dimadl/cosmo-mobilus-mqtt-adapter/src/ha_mqtt/HAMQTTShutterControl.h

#ifndef HA_MQTT_SHUTTER_CONTROL_H
#define HA_MQTT_SHUTTER_CONTROL_H

#include "./shutter/HAMQTTShutter.h"
#include "CosmoMobilusHardwareAdapter.h"
#include "HAMQTTHealthCheck.h"
#include "./mqtt_client/MQTTClient.h"

#define FULLY_OPENED 100
#define FULLY_CLOSED 0

#define EEPROM_SIZE 8
#define ADDRESS_POSITION 8

class HAMQTTShutterControl
{

public:
    static HAMQTTShutterControl *instance;

    HAMQTTShutterControl(MQTTClient &client, CosmoMobilusHardwareAdapter &hardware);
    void begin();
    void registerShutter(uint8_t index, HAMQTTShutter *shutter);
    void initConnection();

private:
    MQTTClient &_client;
    CosmoMobilusHardwareAdapter &_hardware;

    HAMQTTHealthCheck *healthCHeck = new HAMQTTHealthCheck();

    const char *topic_ha_status = "homeassistant/status";
    const char *topic_ha_control_command = "cosmo-ha-adapter/command";

    HAMQTTShutter *shutters[8] = {nullptr};
    uint8_t latestShutterPositions[8];

    // internal state of the control
    uint8_t currentPosition;

    void onMqttMessage(const MqttMessage &msg);

    // Methods
    void setCurrentPosition(uint8_t currentPosition);
    uint8_t getCurrentPosition();

    void moveToShutterIndex(uint8_t shutterIndex);

    void moveToPosition(uint8_t shutterIndex, uint8_t requestedPosition);

    void openAndDelay(HAMQTTShutter *shutter, uint16_t time, bool doPressStop);
    void closeAndDelay(HAMQTTShutter *shutter, uint16_t time, bool doPressStop);
    void moveControlForward(uint8_t diff);
    void moveControlBackward(uint8_t diff);
    void close(HAMQTTShutter *shutter);
};

#endif // HA_MQTT_SHUTTER_CONTROL_H
